jaspercurry/sand-cube/workbench/designs/deferred_integral_front_bottom_hatch/brief.md

# Deferred integral-front / bottom-hatch brief

That's awesome thank you. I think there's one more pair that I wanted. Maybe I already have it. You tell me.

I just want the latest version of the enclosure that has the baffle and the enclosure that fit together and that have the smooth seam on all four corners. I say this because I'm gonna use that one as the external package when I decide to put a hatch in the bottom of the face and try two different variants. This one is important because I wanna put it together and fuse those faces together and then get the seam gone but the overall package should remain the same, including the bottom corner part, because I think this is the right one too. If I'm going to have the baffle stay in place then I don't need the bottom flat face on the baffle or whatever. This is the one I'm going to use to power the hatch project. I need you to find that for me and write me one more little prompt with that as well.
