jaspercurry/sand-cube/workbench/designs/deferred_integral_front_bottom_hatch/feedback.md

# Feedback log

## 2026-07-22 — full-perimeter package inventory

- User identified a second enclosure direction: retain the original full
  exterior package and all four smooth/sculpted corners, make the front baffle
  permanent, remove the front seam, and later explore bottom-hatch variants.
- The latest surviving full-perimeter reference was identified as the
  `lightweight_coherent_closure` bucket, baffle, and installed assembly. The
  later flat-bottom/hybrid artifacts were explicitly excluded from this
  branch.
- Exact artifact paths, hashes, STEP checks, owning source, nested-seam
  ancestor, and build-freshness caveat were recorded in `source_manifest.md`.
- No existing source or CAD geometry was changed, rebuilt, fused, or rendered.
- The future prompt requires a source-level monolithic construction before the
  nested split, rather than a naïve union of separated STEP solids across the
  modeled gasket gap. It also defers tube/resonator repackaging until the
  integral enclosure and hatch architecture are accepted.
