jaspercurry/sand-cube/workbench/designs/deferred_port_tube_resonator/brief.md

# Deferred bass-reflex tube and resonator brief

The last thing is there are two other files that I think are really important to me:
- The tube iterations I've been doing for the base reflex port. That's really important and part of that but I think it's got a separate part of the file system. There's the resonator, right, and that's to help remove resonant frequencies. That is part of kind of the tube structure.
- Can you also find those and make a secondary prompt? Right now I don't want to mess with them. I just want to get all the code to help make them and get it set aside in a good spot. I'm going to come back to it once the fundamentals of the enclosure are nailed down and then we can manipulate the tubes and everything to fit the finalizing closure.
