jaspercurry/sand-cube/workbench/designs/deferred_port_tube_resonator/feedback.md

# Feedback log

## 2026-07-22 — deferred inventory

- User identified the bass-reflex tube iterations and the mode-suppressing
  resonator as important work to preserve but explicitly deferred all geometry
  changes until the enclosure and closure fundamentals are final.
- The tube lineage, resonator lineage, exact current working-tree source
  hashes, current integrated artifacts, latest Rev D artifacts, diagnostics,
  and the Rev C/Rev D integration boundary were recorded in
  `source_manifest.md`.
- Existing source was left in its cataloged experiment directories. No source
  was reset, moved, copied, or edited, and no CAD model, sidecar, viewer, or
  render was generated.
- A self-contained future-agent prompt was written to `resume_prompt.md` with
  a strict final-enclosure gate and measurable restart criteria.
