jaspercurry/sand-cube/workbench/designs/canonical_working_set/horn/links/horn_work_summary.md

../../../../../docs/horn-print-and-viewer-work-summary.md
