jaspercurry/sand-cube/workbench/designs/le_cleach_horn_190/variants/rollback_140/brief.md

# 140° variant — user brief

So you can see that we have a LeClesh horn or a bunch of LeClesh horn variants here in the repo. Could you look at them? I think there's one most recent one that we did actually use the proper LeClesh spreadsheet to inform and I'd love your help to make a new version of a LeClesh horn that matches the new external dimensions of the enclosure I'm working on.

That enclosure is still being revised but you'll see it in the folder and it's, I believe, 190 mm square so I need the diameter of our new LeClesh horn to also be 190 mm square. I'm using a base reflex tube now to hold up the compression drivers and mount and I think it means that the compression driver is going to potentially be a little bit farther back but maybe not actually. We're gonna keep the length of the horn as is for right now and then we'll revise the length and just update the calculation because I understand length is one of many inputs to the LeClesh function.

Let's just get started now. Maybe if you wanna engineer it in a way, you could solve for LeClesh horn with a given length and then that will make it easy to update in the future. Can you help me with this?
