jaspercurry/sand-cube/workbench/designs/le_cleach_horn_190/variants/rollback_140/feedback.md

# 140° variant feedback chronology

## 2026-07-23 — baseline identification

- The repository contains two different profile methods in
  `src/features/horn.py`: the older `legacy_recurrence` and the exact
  `le_cleach_2007` spreadsheet recurrence added in commit `d767489`.
- The stable `src/final_horn.py` still selects the older default method.
- The most recent matching horn is owned by the 190-by-190-by-210
  single-circular-port study. Its stored diagnostics report:
  - 190.0001119 mm physical rolled envelope;
  - 186.130 mm acoustic mouth;
  - 82.3821368 mm axial length;
  - 1002.0056 Hz solved profile cutoff;
  - wavefront factor T = 0.49437398987356584;
  - exact 2007 spreadsheet recurrence;
  - 0.0015091 mm maximum sampled spline deviation.
- Direction: preserve that geometry as the baseline, create a standalone
  candidate, and replace the hand-pinned T value with a deterministic solve
  from the named axial-length target.

## 2026-07-23 — standalone candidate checkpoint

- Production build job:
  `20260723T193247-build-f5f67ed6c8`.
  - Worker PID: 72479.
  - Elapsed: 23.225 seconds.
  - Peak RSS: 0.70 GiB.
  - Exit status: completed.
  - Published outputs: two.
  - Cleanup succeeded and no owned orphan processes remained.
- Exact artifact:
  `build/workbench/le_cleach_horn_190/le_cleach_horn_190.step`.
- STEP SHA-256:
  `56b793cb82df63e898ec8039e0353858817101880e84a87a588f9fb55f180df5`.
- The new inverse solve uses `target_axial_length` as the independent input and
  produced:
  - T = 0.49437398761510853;
  - profile cutoff = 1002.0055766296128 Hz;
  - axial length = 82.38213689951849 mm;
  - spreadsheet row step = 0.04623792275746711 mm;
  - 3020 exact recurrence samples.
- Geometry checks:
  - 190.0001119 mm maximum physical rolled envelope;
  - 186.130 mm acoustic mouth;
  - 8.000 degree CAD throat tangent;
  - 140.000 degree recurrence and CAD terminal tangent;
  - 0.0015091 mm maximum sampled recurrence-to-CAD spline deviation;
  - one valid solid before and after STEP round-trip;
  - exactly two 6.6 mm cylindrical bolt-hole faces, with the three-hole pattern
    disabled.
- STEP audit job `20260723T193323-audit-step-1bc2ce0d09` found one solid, one
  shell, 15 faces, zero boundary edges, zero non-manifold edges, no
  self-interference, and no offset surfaces.
- The hash-matched topology sidecar was regenerated by job
  `20260723T193340-text-to-cad-artifacts-a684077a1c`; it reports 15 mapped
  faces, 28 mapped edges, and zero unmapped surface edges.
- Agent visual review:
  - `snapshot-isometric_20260723T193351Z.png` shows a symmetric rolled-back
    flare, smooth throat-to-mouth shading, the intended two-hole flange, and
    no visible crack or surface collapse.
  - `snapshot-meridian-section_20260723T193404Z.png` shows the expected
    rolled-back meridian and constant wall, but the line renderer omits pieces
    of coincident/shared boundaries near the throat.
  - The final-STEP center-plane diagnostic
    `meridian_diagnostics.json` resolves that visual ambiguity: exactly two
    valid positive-area section faces and exactly two closed wires, one per
    side of the axis. The apparent section gaps are rendering omissions, not
    acoustic-path openings.
- Remaining design decision: driver and port-tower setback/placement remains
  intentionally unfrozen until the enclosure support revision is ready.

## 2026-07-23 — family promotion

- Reorganized entrypoint:
  `workbench/designs/le_cleach_horn_190/variants/rollback_140/build.py`.
- Reorganized artifact:
  `build/workbench/le_cleach_horn_190/variants/rollback_140/le_cleach_horn_190_rollback_140.step`.
- Build job `20260723T200810-build-13d1c87caa` completed successfully in
  22.172 seconds with 0.69 GiB peak RSS, published two outputs, cleaned its
  workspace, and left no owned orphan processes.
- Accepted dimensions, solver values, and topology were reproduced.
- Current STEP SHA-256:
  `3892b70ebf13550881996c886a40a01b1dc89d3132df7162dc935a15d1513fff`.
- Topology audit job `20260723T200914-audit-step-b3bda2ced0` passed.
- Sidecar job `20260723T200954-text-to-cad-artifacts-04704fc492` passed.
- Snapshot job `20260723T201018-text-to-cad-artifacts-957d407ae4`
  reproduced the accepted smooth, symmetric isometric appearance.
