jaspercurry/sand-cube/workbench/designs/le_cleach_horn_190/variants/rollback_160/brief.md

# 160° rollback variant — user brief

## User request

> How hard would it be to increase the rollback? I think right now it's got like a 140° angle for that rollback. What would a 160° look like? Would that be hard for you to do?

## Working interpretation

“Rollback” is the terminal wall angle measured from the horn axis, matching the
existing `exit_angle_deg` parameter. The current 140° horn remains the baseline;
this iteration creates a separate 160° comparison candidate.

## Frozen dimensions

- Physical X/Y envelope: 190.0 mm square
- Acoustic axial length: 82.38213681735276 mm
- Throat diameter: 25.4 mm
- Wall thickness: 3.2 mm
- Throat angle: 8°
- Existing DE250 two-hole mounting geometry
- Existing flange and throat-spigot geometry

Driver/enclosure placement is intentionally deferred. This comparison isolates
the rollback-angle change.
