jaspercurry/sand-cube/workbench/designs/canonical_working_set/acoustics/bass_reflex_tube/reference_evidence/manifest.md

# Bass-reflex tube reference evidence

These files are immutable, hash-bound review evidence copied from the
read-only intake checkout on 2026-07-22. They are not authoritative source.
The `Original SHA-256 = promoted SHA-256` column records both hashes; identity
was verified after the copy.

| File | Original repository path | Original SHA-256 = promoted SHA-256 | Bytes | Recorded producer | Approved semantic contribution | Caveat |
|---|---|---|---:|---|---|---|
| `sand_cube_190x210_single_oval_port_internal_tube.step` | `build/sand_cube_190x210_internal_squat_absorber_rear_corners_parabolic_side_g1_lightweight_coherent_closure/sand_cube_190x210_single_oval_port_internal_tube.step` | `5667fa455b81f8fc0f9a4645677a359f7b9072f0750eaff4f39a2099255fa19c` | 1,094,673 | Lightweight coherent-closure publication of the `sand_cube_190x210_single_oval_port` lineage | Selected internal oval tube geometry | Copied from a later enclosure build; use the recorded route-source chain to reproduce and compare |
| `diagnostics.json` | `build/sand_cube_190x210_internal_squat_absorber_rear_corners/diagnostics.json` | `dce0dcd3452ee8a98cea69073a52b3c3a299e42ec1a0e5bd716197cbf27af913` | 51,330 | `experiments/sand_cube_190x210_internal_squat_absorber_rear_corners/generate_sand_cube_190x210_internal_squat_absorber_rear_corners.py` | Route measurements for the selected rear-corner stage | Describes an earlier route stage, not the copied lightweight artifact; embedded absolute build paths are historical records, not portable links |
