jaspercurry/sand-cube/workbench/designs/canonical_working_set/enclosures/removable_front_baffle/reference_evidence/manifest.md

# Removable-front reference evidence

These files are immutable, hash-bound review evidence copied from the
read-only intake checkout on 2026-07-22. They are not authoritative source and
must not be treated as proof that the landed Python rebuilds identical
geometry. The `Original SHA-256 = promoted SHA-256` column records both hashes;
identity was verified after the copy.

| File | Original repository path | Original SHA-256 = promoted SHA-256 | Bytes | Recorded producer | Approved semantic contribution | Caveat |
|---|---|---|---:|---|---|---|
| `clean_corner_hunks_bucket.step` | `build/workbench/enclosure_baffle_recovery/clean_corner_hunks_candidate_viewer/clean_corner_hunks_bucket.step` | `eaeed68103e3110ca3e888ece90002a7f2f98a8b174fab5906e7fb0bd9350b97` | 4,310,535 | `workbench/designs/enclosure_baffle_recovery/build_step_derived_clean_hunks_candidate.py` | Curved seat with the four unwanted corner/fill-port hunks removed | STEP-derived disposable candidate; coordinated source build did not complete |
| `hybrid_seam_assembled.step` | `build/sand_cube_190x210_internal_squat_absorber_rear_corners_parabolic_side_g1_simple_tongue_groove_baffle/hybrid_seam_assembled.step` | `90558975e0e8fb735534b53a73eb7970d3bdddd6aeda34fb821380915877bab0` | 11,094,222 | Historical run of the simple tongue-and-groove lineage; exact producing source revision is not preserved | First/larger solid is the complementary flat-bottom bucket reference | Archived two-solid assembly; standalone extraction was invalid and was not published |
| `simple_tongue_groove_baffle.step` | `build/sand_cube_190x210_internal_squat_absorber_rear_corners_parabolic_side_g1_simple_tongue_groove_baffle/simple_tongue_groove_baffle.step` | `23c4d67927bbec6702c300c9912a7542383de093940378184b3d932fee3971c2` | 7,245,209 | `experiments/sand_cube_190x210_internal_squat_absorber_rear_corners_parabolic_side_g1_simple_tongue_groove_baffle/generate_sand_cube_190x210_internal_squat_absorber_rear_corners_parabolic_side_g1_simple_tongue_groove_baffle.py` | Genuinely planar full-width print edge and associated baffle material ownership | Approval does not extend to its tongue-and-groove or other seam details |
