jaspercurry/sand-cube/workbench/designs/canonical_working_set/brief.md

# Brief

> Yes that's exactly right. It's just a trustworthy design map, ideally with these fundamental atomic models and code or whatever moved to the directory that we can easily work on

The detailed design intent is already preserved verbatim in these existing
records and is incorporated here by reference:

- `workbench/designs/enclosure_baffle_recovery/brief.md`
- `workbench/designs/deferred_integral_front_bottom_hatch/brief.md`
- `workbench/designs/deferred_port_tube_resonator/brief.md`

This iteration organizes those accepted handoffs without changing geometry.
