jaspercurry/sand-cube/workbench/designs/canonical_working_set/acoustics/d_squat_resonator/reference_evidence/manifest.md

# D-squat resonator reference evidence

These files are immutable, hash-bound review evidence copied from the
read-only intake checkout on 2026-07-22. They are not authoritative source.
The `Original SHA-256 = promoted SHA-256` column records both hashes; identity
was verified after the copy.

| File | Original repository path | Original SHA-256 = promoted SHA-256 | Bytes | Recorded producer | Approved semantic contribution | Caveat |
|---|---|---|---:|---|---|---|
| `internal_d_squat_absorber_installed.step` | `build/sand_cube_190x210_internal_squat_absorber_rear_corners_parabolic_side_g1_lightweight_coherent_closure/internal_d_squat_absorber_installed.step` | `a16aeb1b440ef94a3cb208e4388eeac9c2acec238791fde4c33ebf0a3a4788ce` | 975,988 | Lightweight coherent-closure publication of the internal-absorber lineage | Rev C installed placement inside the enclosure | Placement evidence only; not a standalone manufacturing artifact |
| `port_absorber_d_squat_rev_d_assembly_finished_reference.step` | `build/sand_cube_190x210_port_absorber_slotted_d_squat_rev_d/port_absorber_d_squat_rev_d_assembly_finished_reference.step` | `3ed5020cf53511f676ec3ed9a709d44a81e112f5b91fb1757dfbf09f4fcb33da` | 953,398 | `experiments/sand_cube_190x210_port_absorber_slotted_d_squat_rev_d/generate_port_absorber_slotted_d_squat_rev_d.py` | Rev D assembled reference | Frozen comparison artifact; rebuild identity not checked during intake |
| `port_absorber_d_squat_rev_d_print_layout.step` | `build/sand_cube_190x210_port_absorber_slotted_d_squat_rev_d/port_absorber_d_squat_rev_d_print_layout.step` | `5936001348ce7d146519a8836507d6800b703cce71f0a3d808f2df20f818d76e` | 811,849 | Same Rev D generator | Rev D print-layout reference | Layout reference only; no slicer settings are implied |
| `diagnostics.json` | `build/sand_cube_190x210_port_absorber_slotted_d_squat_rev_d/diagnostics.json` | `b2486dd92bda832be28b2d1e0b54666c06e0641924a2231283b8c37717a28c01` | 18,725 | Same Rev D generator | Exact recorded Rev D branch inputs and measurements | Describes the copied output, not a fresh landing build |
