jaspercurry/sand-cube/workbench/designs/canonical_working_set/enclosures/integral_front_bottom_hatch/reference_evidence/manifest.md

# Integral-front / bottom-hatch reference evidence

These files are immutable, hash-bound review evidence copied from the
read-only intake checkout on 2026-07-22. They are not authoritative source and
the landed generator is newer than these artifacts. The
`Original SHA-256 = promoted SHA-256` column records both hashes; identity was
verified after the copy.

| File | Original repository path | Original SHA-256 = promoted SHA-256 | Bytes | Recorded producer | Approved semantic contribution | Caveat |
|---|---|---|---:|---|---|---|
| `centered_captive_nut_bucket.step` | `build/sand_cube_190x210_internal_squat_absorber_rear_corners_parabolic_side_g1_lightweight_coherent_closure/centered_captive_nut_bucket.step` | `39e6b2d95317d2348afd992ceda2e98d16a383820a3846737e21228ef1c41486` | 4,583,193 | `experiments/sand_cube_190x210_internal_squat_absorber_rear_corners_parabolic_side_g1_lightweight_coherent_closure/generate_sand_cube_190x210_internal_squat_absorber_rear_corners_parabolic_side_g1_lightweight_coherent_closure.py` | Full-perimeter bucket reference | Hash-bound review output from a coordinated job whose later preview-only cutaway failed |
| `centered_captive_nut_baffle.step` | `build/sand_cube_190x210_internal_squat_absorber_rear_corners_parabolic_side_g1_lightweight_coherent_closure/centered_captive_nut_baffle.step` | `1dd518458c8fed6792c4acd91f0717b353288c18e49c5b1c6ba31f2c9cc6af03` | 8,687,475 | Same lightweight coherent-closure generator | Full-perimeter baffle reference | One valid solid, but source/artifact identity has not been re-established |
| `centered_captive_nut_assembled.step` | `build/sand_cube_190x210_internal_squat_absorber_rear_corners_parabolic_side_g1_lightweight_coherent_closure/centered_captive_nut_assembled.step` | `4595684887c4fb239dd8fefaeb7307a797c3673281df19f3d709b659b3440bf2` | 13,810,764 | Same lightweight coherent-closure generator | Installed-fit reference | Nine valid solids include gasket and hardware references; not a print part |
| `diagnostics.json` | `build/sand_cube_190x210_internal_squat_absorber_rear_corners_parabolic_side_g1_lightweight_coherent_closure/diagnostics.json` | `7194ac15b3c78e272ae60d9b1115be6129f0fdfbfd7cbfdcef32593cddbff04d` | 70,504 | Same lightweight coherent-closure generator | Recorded geometry, installed-volume, and tuning measurements for this evidence set | Describes the copied output, not a fresh landing build; embedded absolute build paths are historical records, not portable links |
