jaspercurry/sand-cube/objects/GX16.stp

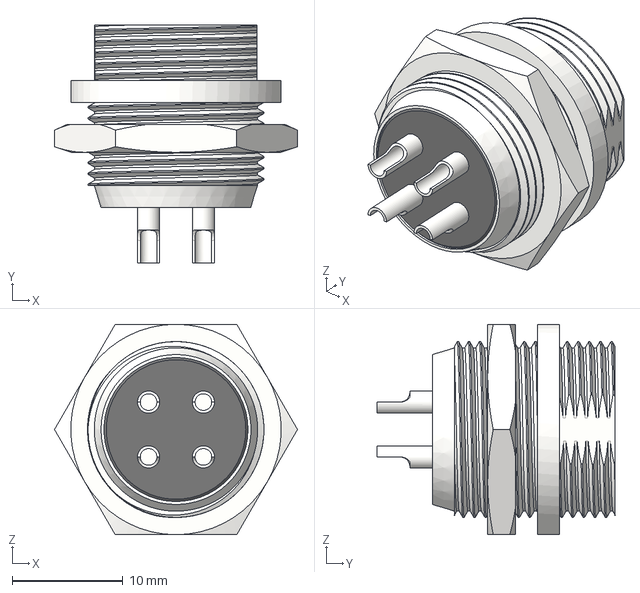
[picture p8: CAD file, 2026-05-16]
objects/GX16.stp
21.9 x 21.5 x 19.0 mm
