jaspercurry/sand-cube/objects/E180HE-PR.step

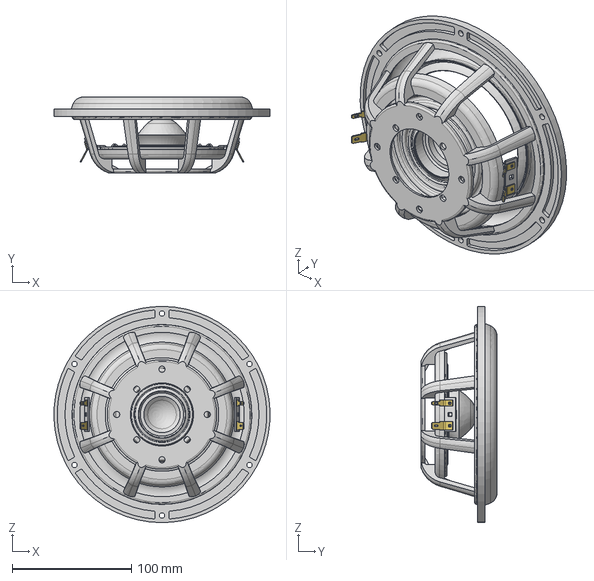
[picture p9: CAD file, 2026-05-16]
objects/E180HE-PR.step
181.4 x 64.0 x 181.5 mm
