jaspercurry/sand-cube/objects/E150HE-44.step

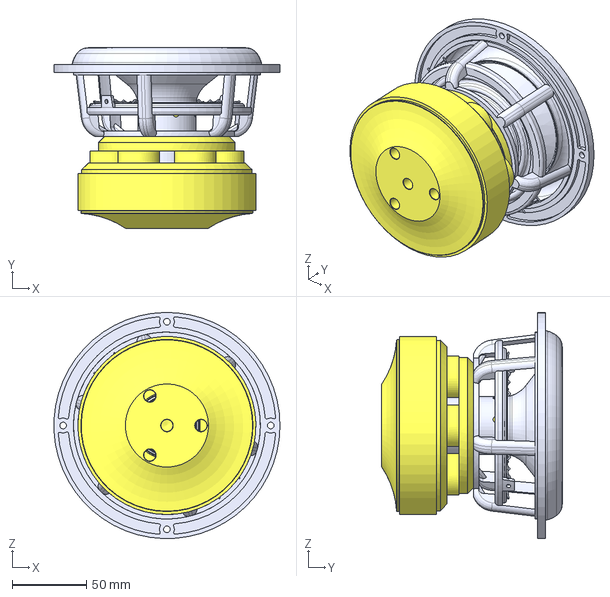
[picture p10: CAD file, 2026-05-16]
objects/E150HE-44.step
152.4 x 121.7 x 152.4 mm
6_0_____CAST_BFGT__0502A__REV_
38MM_VCDDGATE_REV-A1_A_
