jaspercurry/sand-cube/workbench/designs/cad_feedback_loop_rollout/baseline-step-sha256.txt

# cad_runner job 20260723T211801-generate-sand-cube-190x210-single-oval-port-43ef802b42
# elapsed_seconds=105.594 peak_rss_bytes=885719040 cleanup_reaped=true orphans=0
24aaafefc60ea8238387eda621a12f7032a976b9188f46074b07b13557281170  sand_cube_190x210_single_oval_port_airway.step
d2c9fd17aabc00872acaa5be44ef441448414dafe2ca892b0e238d612991c1ab  sand_cube_190x210_single_oval_port_assembly.step
c17d0cca77e7d6511208e47e2d88b29f5db16450701179dea7fc73e638ddfbcf  sand_cube_190x210_single_oval_port_base.step
9fbc8a8fa89885bc039d770e2adb8f656937f64abc07ef26626db2d13dcee0e6  sand_cube_190x210_single_oval_port_cutaway.step
1eded4b9dbb2024c458eacac672d0171ea5e3b9c020a4288703b839c4cc6b5ee  sand_cube_190x210_single_oval_port_gx16.step
7ab03b2d47b9a56e9d0683fd22d489a1926dfea0171c865913ad98613fba6d2a  sand_cube_190x210_single_oval_port_hardware_check.step
d57ad948c78ecf9863ef34f7386df557dd5d2980e16d1ca6ab15d5596d3bbd18  sand_cube_190x210_single_oval_port_horn.step
aa3d88f1fabd3380dd585740d99e04c962fddda5c6d0883d536e1b3d038fcfb8  sand_cube_190x210_single_oval_port_internal_tube.step
80dc810c5478aa5d6305cd482ae8f11e18c1cc125b376f5274c5cfab621c1662  sand_cube_190x210_single_oval_port_tower.step
