jaspercurry/sand-cube/experiments/sand_cube_190x210_internal_squat_absorber_rear_corners/README.md

# Rear-corner sweep / exact rear-flush absorber variant

This isolated variant preserves all preceding studies. It routes the 40 mm
circular port through a broad R75 lower-left rear sweep and an R50 lower-right
rear rise, then uses four rotated R35.7 elbows around the unmodified 56 mm squat
absorber cartridge.

The absorber D-flat has exact nominal contact with the rear acoustic face. No
printing relief, absorber mounting tab, or enclosure mounting node is modeled.
