jaspercurry/sand-cube/workbench/designs/atomic_characterization_refactor/README.md

# Atomic characterization/refactor

Status: **Phase B implementation, strict final acceptance, exact visual review,
and independent adversarial re-review are complete with no unresolved
actionable findings in the agreed landing scope.**

The user accepted the Phase A visual evidence and authorized Phase B. The
metadata-only `family.coordinate_contract` pilot is complete. The user then
explicitly instructed the agent to record but not pause at later checkpoints.
No removable-front references have been reconciled, no Variant I geometry has
been created, and no deferred component has been integrated.

## Governing records

- `brief.md` — verbatim user request; do not edit
- `contract.md` — interpreted operational boundary
- `feedback.md` — chronological work log
- `atomic_manifest.json` — authoritative input, atom, evidence and checkpoint
  description
- `workflow-card.md` — concise resume state for the current implementation
- `current-baseline-evidence.json` — durable current-base fit/equivalence facts
- `variant-r-producer-source-closure.json` — committed projection of the exact
  authoritative-input producer, toolchain and complete live source closure
- `variant-r-release-source-closure.json` — committed projection of the exact
  release commit, release-job JSON, nine bound model artifacts and all loaded
  release dependencies
- `final-acceptance-evidence.json` — compact final jobs, measurements, hashes,
  visual provenance and review disposition
- `independent-review.md` — initial findings, amendments, and final
  no-unresolved-findings disposition
- `render_phase_a_reports.py` — deterministic Markdown projection
- `coordinate_contract.json` — staged verification contract for the first atom

## Generated checkpoint views

- `inventory.md`
- `atomic_map.md`
- `compatibility_matrix.md`
- `dependency_graph.md`
- `baseline_report.md`
- `printability_report.md`
- `pilot_report.md`

## Architecture proposal

- `proposed_architecture.md`

## Current geometry boundary

The failed rail reproduction recorded during the earlier Phase B pilot is
historical. Commits through `789cf7f` repaired that deterministic failure and
established the current flat-bottom Variant R closure. On exact combined base
`c25cddb`, the active Python source and validator reproduce the accepted bucket,
baffle, and six protected sections with zero bidirectional material difference
at `1e-5 mm³`, matching topology and mass properties, zero overlap, and passing
STEP round-trips.

The cataloged `scripts/generate_variant_r.py` entrypoint makes the formerly
ignored base input portable. It extracts exact geometry commit `789cf7f`,
applies one hash-bound capture-only overlay at the accepted construction
boundary, verifies the complete STEP DATA section, reproduces the accepted
file serialization, and publishes both the base and a current attestation
through `cad_runner`. The latest producer binds 57 loaded repository sources,
including all 33 loaded generator stages. Release evidence is collected only
after geometry in a separate observational job, preserving the exact accepted
validator execution path. It binds release commit `d114d79`, the exact release
job record, nine model artifacts, 62 loaded repository sources, 58
geometry/parameter sources and all 33 loaded generator stages. Every dependency
byte is verified at that commit. The historical release job did not itself
record whole-tree cleanliness, and the committed record says so instead of
inventing that claim. The final strict job passes both complete parts and six
protected sections with zero bidirectional material delta and unchanged
diagnostics. Committed closure projections preserve those exact facts without
treating ignored `build/` files as current.

The active architecture has explicit owners for datums, pure parameters,
print contracts, Variant R seam/bottom composition, the independent future
Variant I interface, generated input/provenance, deterministic measurements,
native-free equivalence policy, STEP export/round-trip, artifacts, verification
and thin entrypoints. Variant I has no geometry and imports no Variant R owner.

The refactor's accepted geometry intentionally preserved its historical flat-
bottom relationship. A separate, explicitly authorized production iteration
has since replaced the whole-part splice with the continuous exact-edge donor
and a baffle-only sole trim. Its exact twelve internal bucket-only
micro-omissions are recorded fail-closed in
`workbench/designs/variant_r_no_splice_production/`; the refactor evidence here
remains the immutable pre-correction baseline.
