jaspercurry/sand-cube/workbench/designs/atomic_characterization_refactor/atomic_map.md

<!-- Generated by render_phase_a_reports.py from atomic_manifest.json. Do not edit by hand. -->

# Atomic ownership map

Authority: `atomic_manifest.json`.

Current execution overlay: **FINAL FORCED RELEASE EQUIVALENT; VISUAL EVIDENCE INSPECTED; INDEPENDENT REVIEW PENDING**. Rows retain historical characterization; the overlay supersedes old operational blocker wording.

| Semantic ID | Owner | Current owner/source | Dependencies | Mates | Baseline | Shareability | Readiness | Conflicts |
|---|---|---|---|---|---|---|---|---|
| family.coordinate_contract | shared enclosure-family layer | src/enclosure_family/datums.py | — | — | native-free coordinate contract and full current Variant R strict release pass | yes; one explicit 190x210 family datum owner now exists | implemented and verified | legacy 203 mm project parameters are a different family contract |
| family.exterior_envelope | Variant R foundation; possible family sharing remains unproved | immutable accepted foundation producer plus explicit Variant R composition | family.coordinate_contract | — | current Variant R full-part bounds/topology/mass and zero-material-delta proof pass | intended, not yet proven semantically identical | verified for Variant R; do not promote to shared geometry until an independent Variant I proves identical semantics | legacy 203 mm production enclosure and 222.463 mm horn mouth belong to different packages |
| family.exterior_shell | Variant R foundation; possible family sharing remains unproved | immutable accepted foundation producer behind VariantRFoundation | family.coordinate_contract<br>family.exterior_envelope | — | current Variant R complete bucket and protected sections pass strict equivalence | possible only if Variant I exterior is proven identical | verified for Variant R; family extraction is deferred until cross-variant semantic identity can be proved | root project 3/12/3 contract is not this 2/3/2 study stack |
| family.inner_wall_sand_void | Variant R foundation; future sharing unproved | single-oval-port base and conformal-inner-wall stage | family.exterior_shell | family.fill_blisters_passages | current Variant R validator proves zero fill blockage, closed non-fill sand cap and exact protected geometry | intended but unproved | verified as current Variant R foundation behavior; not promoted as shared Variant I geometry | 3 mm void differs from repository legacy 12 mm void |
| family.rear_face | Variant R foundation with Variant R print-contract consumer | single-oval-port base plus rear-corner/conformal detail | family.exterior_shell<br>family.inner_wall_sand_void | — | current Variant R bounds and rear-body retention diagnostics pass | geometry may be shared; print semantics are variant-specific | verified for Variant R; print semantics remain variant-specific | future I does not use rear face as bed datum |
| R.front_service_opening | Variant R | VariantRFoundation implemented by the active compatibility adapter and consumed by src/enclosure_family/variant_r/assembly.py | family.exterior_shell<br>family.inner_wall_sand_void | R.baffle_body<br>R.front_bulkhead_gasket_support | current bucket/baffle parts, service opening retention diagnostics and protected sections pass | no | verified Variant R foundation boundary | accepted lower boundary is preserved exactly; correction is a later geometry task |
| R.front_bulkhead_gasket_support | Variant R | VariantRFoundation implemented by the active compatibility adapter; verification policy in src/enclosure_family/variant_r/verification.py | R.front_service_opening<br>family.inner_wall_sand_void | R.baffle_body<br>R.gasket_land_compression | current gasket support ratios are 1.0 against a 0.985 minimum; corner and fill checks pass | no; removable-joint support | verified Variant R foundation boundary | physical gasket compression and printed support behavior remain untested |
| R.sculpted_lrt_seam | Variant R | src/enclosure_family/variant_r/seam.py composed by src/enclosure_family/variant_r/assembly.py | R.front_service_opening<br>R.front_bulkhead_gasket_support | R.baffle_body<br>R.gasket_land_compression | current source generation plus strict zero-material-delta proof for full parts and protected seam sections | no | extracted and strict-equivalence verified | the accepted current flat-bottom imperfection is protected baseline behavior |
| R.bottom_material_ownership | Variant R | src/enclosure_family/variant_r/bottom_ownership.py composed by src/enclosure_family/variant_r/assembly.py | R.front_service_opening<br>family.exterior_shell | R.baffle_body | current source generation plus strict zero-material-delta proof for full parts and flat-bottom/corner protected sections | no | extracted and strict-equivalence verified | accepted current missing-material relationship remains intentionally unfixed |
| R.baffle_body | Variant R | src/enclosure_family/variant_r/assembly.py over VariantRFoundation, seam.py and bottom_ownership.py | R.sculpted_lrt_seam<br>R.bottom_material_ownership<br>family.driver_interface | R.front_service_opening<br>R.front_bulkhead_gasket_support | one valid solid; strict topology/bounds/volume/area/center-of-mass and zero-material-delta proof pass | no | current Variant R geometry verified | accepted flat-bottom/missing-material relationship remains intentionally unfixed |
| R.flat_baffle_print_edge | Variant R | src/enclosure_family/variant_r/bottom_ownership.py with print contract in variant_r/print_contracts.py | R.baffle_body<br>R.bottom_material_ownership | — | current bottom section is strict-equivalent; planar contact area is 2277.9500229303967 mm2 with brim assumed | no | geometry and analytic contact verified; physical adhesion unverified | known missing-material relationship is preserved |
| family.driver_interface | current Variant R foundation; future family sharing unproved | hooked/lightweight baffle and fairing ancestors | family.coordinate_contract | deferred.horn_interface<br>deferred.bracket_interface | current baffle bore/fairing geometry is included in the strict full-part equivalence proof | intended if both variants use the same driver and front profile | verified for current Variant R only | future horn package not accepted |
| R.gasket_land_compression | Variant R | VariantRFoundation plus src/enclosure_family/variant_r/parameters.py and verification.py | R.sculpted_lrt_seam<br>R.front_bulkhead_gasket_support<br>R.baffle_body | R.sculpted_lrt_seam<br>R.baffle_body | 1.0 mm compression knob and 1.0/1.0 bucket/baffle support ratios reproduce current diagnostics exactly | no | geometry verified; physical gasket behavior unverified | material compression specification and leak test remain absent |
| R.corner_sealing | Variant R | VariantRFoundation with deterministic checks in the current validator | R.front_bulkhead_gasket_support<br>R.gasket_land_compression | family.fill_blisters_passages | zero unclosed outside-gasket and baffle-corner volumes; four baffle corner closures | no | current Variant R geometry verified | physical sealing remains untested |
| family.fill_blisters_passages | current Variant R foundation; future variant-specific termination remains separate | front-fill perimeter-seal and lightweight closure | family.inner_wall_sand_void<br>R.front_bulkhead_gasket_support | family.inner_wall_sand_void<br>R.corner_sealing | current fill passage blockage is 0.0 mm3 and both passages reach the live sand void | shared upstream routing only if termination semantics are separated | verified for current Variant R; not promoted as shared Variant I geometry | front termination differs fundamentally between removable and integral fronts |
| family.braces_supports | current Variant R immutable foundation; future shared ownership unproved | conformal_full_system and lightweight _coherent_internal_braces | family.inner_wall_sand_void<br>deferred.tube_interface | family.inner_wall_sand_void | the accepted coherent-brace foundation is reproduced exactly by the portable producer and retained by the current bucket | not proven; front supports differ by variant | verified for current Variant R foundation; no shared Variant I brace owner is asserted | physical support/print behavior remains unverified |
| family.support_sensitive_transitions | family metadata candidate | not explicit; distributed across bulkhead, fairing, rails and fill passages | family.braces_supports<br>family.fill_blisters_passages | — | visual/section characterization only | neutral predicates can be shared; geometry is variant-specific | metadata-only candidate | current sources do not encode a common printable-overhang policy |
| R.bucket_print_contract | Variant R | src/enclosure_family/variant_r/print_contracts.py | family.rear_face<br>family.support_sensitive_transitions<br>R.front_service_opening | — | explicit rear-face-down metadata matches the accepted current artifact; physical seating footprint/flatness remains unverified | no | implemented metadata; physical print unverified | physical print and slicer behavior remain unverified |
| R.baffle_print_contract | Variant R | src/enclosure_family/variant_r/print_contracts.py | R.flat_baffle_print_edge<br>family.support_sensitive_transitions | — | explicit +Z/brim metadata plus measured Z=-91.5 mm contact plane, 2277.9500229303967 mm2 planar area and 187.02097935912883 mm X span | no | implemented and analytically verified; physical print unverified | physical adhesion and slicer behavior remain unverified |
| I.integral_front | Variant I | src/enclosure_family/variant_i/interface.py declares the future independent boundary; geometry intentionally absent | family.exterior_shell<br>family.driver_interface<br>family.fill_blisters_passages | — | does not exist; references are removable-front evidence only | variant-specific composition | future geometry | historic full-perimeter assembly still has separate bucket/baffle and joint hardware |
| I.open_bottom | Variant I | src/enclosure_family/variant_i/interface.py declares future ownership only | I.integral_front<br>family.inner_wall_sand_void | I.hatch_interface | none | no | future geometry | no selected artifact contains this opening |
| I.hatch_interface | Variant I | src/enclosure_family/variant_i/interface.py declares future ownership only | I.open_bottom | I.open_bottom | none | no | future interface only | hatch design expressly outside Phase A/B |
| I.print_contract | Variant I | src/enclosure_family/variant_i/interface.py | I.open_bottom<br>family.support_sensitive_transitions | — | future metadata only; no geometry baseline claimed | no | implemented future metadata; geometry absent | historic references are closed-bottom removable assemblies |
| R.hinge_interface | Variant R | future Variant R owner | R.sculpted_lrt_seam<br>R.baffle_body | R.baffle_body | none; current leaf flags hinge false | no | future interface only | no hinge geometry approved |
| R.fastener_interface | Variant R | future Variant R owner; historical fastener stages are supporting only | R.bottom_material_ownership<br>R.gasket_land_compression | R.baffle_body | historic hardware reference only; current leaf flags screws false | no | future interface only | historical captive-nut geometry is not accepted final behavior |
| deferred.horn_interface | deferred horn owner | src/final_horn.py and src/features/horn.py | family.exterior_envelope<br>family.driver_interface | family.driver_interface<br>deferred.bracket_interface | formula/source reference only; no selected STEP | external interface only | deferred | current mouth exceeds selected 190 mm width |
| deferred.tube_interface | deferred tube owner | rear-corner route source and tube ancestor chain | family.inner_wall_sand_void<br>family.rear_face | deferred.resonator_interface | historic artifact measured; current source/artifact parameter freshness unresolved | external interface only | deferred | historic 40 mm diagnostics versus current approximately 39.24 mm equivalent source parameter |
| deferred.resonator_interface | deferred resonator owner | Rev C modules and Rev D study generator | deferred.tube_interface | deferred.tube_interface | historic STEP/diagnostics measured; sources not run because component is deferred | external interface only | deferred | Rev D is not automatic mechanical replacement for Rev C |
| deferred.bracket_interface | deferred bracket owner | src/features/bracket.py | family.driver_interface<br>deferred.horn_interface | family.driver_interface<br>deferred.horn_interface | not selected for Phase A artifact inventory | external interface only | deferred | future horn/enclosure package unknown |
| deferred.electronics_interface | deferred electronics owner | not selected in canonical enclosure inputs | family.exterior_shell<br>family.inner_wall_sand_void | — | none in Phase A scope | external interface only | deferred | no accepted enclosure package |

Protected invariants, tolerances, print implications, consumers, and candidate references remain in the manifest to keep this view compact.
