jaspercurry/sand-cube/workbench/designs/atomic_characterization_refactor/feedback.md

# Atomic characterization/refactor feedback

This is the chronological Phase A record. Findings below are descriptive; the
authoritative structured facts are in `atomic_manifest.json`.

## 2026-07-23 — task and prompt integrity

- Work began only in the dedicated Codex worktree at
  `/Users/jaspercurry/.codex/worktrees/8b9b/CAD - Enclosure`.
- `HEAD` was
  `905ef31a0bea348b6805a2ef215c75b5a9592168`, the tip used for
  `codex/atomic-characterization-base`; the worktree itself is detached and
  the branch remains checked out in its separate base worktree.
- Local `main` is
  `ea5539f3372e1bad5ad05eba85f4bd9a53e8c868`, and that required commit is an
  ancestor of the task commit.
- The input-landing commit
  `2c94314b8cee90c3733991d48143375227a7d6b8` and its selected files were
  present.
- The complete `brief.md` was read. Its SHA-256 matched
  `7cb5fad7514df1670ba9fd017cce0d44369564018515e3b4ec5be2c55d4bb96e`.
  It was not modified.

## 2026-07-23 — skill, rules and canonical inputs

- The repository-local `speaker-enclosure-cad` skill and its iteration,
  visual-review, toolchain-safety, model-catalog and geometry-gotcha
  references were read and applied.
- Root/scoped `AGENTS.md`, project/catalog/contract files, development and
  verification documentation, every canonical working-set root/component
  document, the complete enclosure recovery record, all selected manifests,
  the active owner/validator/handoff and relevant generator ancestry were read.
- The canonical README/manifests now describe the landed inputs as committed
  and self-contained. Historic feedback retains historic dirty-checkout
  wording for provenance; it is not a current source statement and was not
  rewritten.
- Verification of `reference_checksums.sha256` passed all 30 selected paths.

## 2026-07-23 — pinned tool preflight

- The task reused Python 3.12.13, build123d 0.11.1 and OCP 7.9.3.1 from the
  existing repository virtual environment. No package was upgraded.
- This clean worktree initially lacked ignored local tool state. The exact
  pinned Text-to-CAD 0.3.9 checkout at commit
  `fdbb4b4fb62d95ae298cfe9a46fdc7092bdaf423` was cloned locally into ignored
  `build/` state; its already-installed Viewer and Snapshot runtimes were
  linked from the exact existing checkout. No network download or source-tree
  dependency change occurred.
- `scripts/cad_review.py doctor` passed all pins, catalog, read-only Viewer
  overlay and preferred-port checks.
- Catalog validation passed: 10 primary models and 38 experiment families.
- The native-free lightweight suite passed 82 tests and 19 subtests, including
  76 entrypoint-safety checks.

## 2026-07-23 — ownership and mutation characterization

- The apparent leaf owner is not self-contained. It aliases deep experiment
  modules, temporarily replaces perimeter/joint constants and functions, calls
  the complete ancestor `generate()` chain, and restores globals afterward.
- The semantic pre-split branch is the `full_base` argument entering
  lightweight `_lightweight_common_joint`. That function creates nominal and
  clearance envelopes, partitions bucket and baffle, and then adds gasket
  support, bulkhead, fill paths, bridges and braces.
- Current removable-joint dimensions are distributed: simplified closure owns
  sculpted path values and the corrected 184.3 mm/r7 broad reset; hooked owns
  bed/gasket/shoulder helpers; nested owns the 0.28 mm split envelope;
  lightweight patches the leaf gap to 1.0 mm and owns the bulkhead/support
  composition.
- This confirms that a future Variant I owner must branch semantically before
  the removable partition. The selected “integral” STEP set is still a
  removable bucket, baffle, gasket/hardware assembly and cannot be treated as
  Variant I geometry.

## 2026-07-23 — immutable reference measurements

- Ten selected STEP artifacts were imported and measured read-only with
  Build123d Workbench. Exact volume, surface area, bounds, center of mass and
  topology are recorded in `atomic_manifest.json` and projected into
  `baseline_report.md`.
- The clean bucket is one valid solid at `1,091,181.8588 mm³`; the hybrid
  bottom-ownership assembly is two valid solids, with a
  `1,111,212.8535 mm³` larger bucket and `233,360.5156 mm³` baffle.
- The selected flat baffle is one valid `231,910.4722 mm³` solid spanning
  approximately 190.0021 mm in X. Its accepted contribution remains the
  documented flat full-width edge; the measurement did not independently
  establish a continuous stable bed-contact face and minimum seating area.
- Tube and Rev C/Rev D references measured as valid multi-solid evidence.
  Their geometry was not integrated or refactored.

## 2026-07-23 — source reproduction gate

- A first runner invocation contained an incorrect shortened experiment path
  and stopped before loading source. It is not a CAD result.
- The corrected, catalog-resolved lightweight source was run once through
  `cad_runner` as job
  `20260723T040911-generate-sand-cube-190x210-internal-squat-absorb-603368ef69`.
- After 83.797 seconds and peak RSS 1,290,780,672 bytes, the current source
  failed with:
  `ValueError: rear-ramped longitudinal top rail did not produce one valid solid: 2`.
- The runner published no outputs and reaped its process group. There was no
  blind geometry retry.
- Because the authoritative lightweight base STEP was not produced, the leaf
  validator was not run. The accepted source baseline is therefore
  unreproducible at this commit. Immutable STEP references remain evidence and
  were not promoted as source.

## 2026-07-23 — exact visual evidence

- A byte-identical copy of the clean-bucket STEP was placed under ignored
  `build/workbench/atomic_characterization_refactor/near_perfect_bucket/`.
  It retains SHA-256
  `eaeed68103e3110ca3e888ece90002a7f2f98a8b174fab5906e7fb0bd9350b97`.
- Its Text-to-CAD sidecar has SHA-256
  `609bb53774ab6301a4ad724aeb62d0a0ed7b3600c93528d9502d73d8e5dc5d4b`.
- Initial Snapshot job
  `20260723T042549-text-to-cad-artifacts-55fbbd24c2` stopped before rendering
  because the ignored clean-worktree checkout lacked the already-installed
  pinned Snapshot runtime. After linking that exact runtime, sandboxed job
  `20260723T042612-text-to-cad-artifacts-88542cfab5` was cleanly reaped when
  macOS denied Chromium's MachPort rendezvous. Neither attempt produced an
  image or changed geometry.
- Snapshot job
  `20260723T042632-text-to-cad-artifacts-fe2639776f` completed in 3.095 seconds
  at peak RSS 856,621,056 bytes and produced an isometric plus one YZ center
  section from the same STEP/sidecar.
- The agent inspected both images. The isometric shows one coherent open-front
  bucket, the sculpted perimeter seat, top opening, internal rails/posts and no
  four repeated front corner hunks. The center section shows nested wall/shell
  outlines and isolated ledges, but does not prove gasket compression, lower
  ownership or printable overhang angles.
- A hash-bound read-only Viewer record was written under ignored build
  evidence. No transient Viewer selection token was used as source logic.

## 2026-07-23 — checkpoint decision

- `atomic_manifest.json` records 30 selected inputs and 30 semantic atoms.
- The generated inventory, atom map, compatibility matrix, dependency graph,
  baseline report and printability report all derive from that manifest.
- Phase B is blocked by both the required user gate and the failed source
  baseline. Variant R candidate reconciliation, Variant I geometry, acoustic
  integration and printability redesign remain later work.
- The proposed first pilot after explicit approval is the metadata-only
  `family.coordinate_contract`; no geometry atom should be extracted until the
  source baseline is repaired or an accepted reproducible source boundary is
  deliberately selected.

## 2026-07-23 — Viewer frontend repair

- The user reported that the hash-bound Viewer URL displayed `Not found`.
- The read-only 0.3.9 backend, exact STEP, and exact sidecar were all present.
  Browser inspection was used only because the failure was visible UI routing
  behavior that the server metadata endpoint could not diagnose.
- The clean worktree's ignored pinned Viewer checkout lacked its prebuilt
  `viewer/dist` frontend. The exact existing 0.3.9 frontend from the repository
  tool checkout was linked into that ignored checkout; no package, source,
  geometry, STEP, or sidecar changed.
- After reloading the same tab, the Viewer displayed
  `near_perfect_bucket.step`, its STEP tree, view controls, and release 0.3.9.

## 2026-07-23 — Characterization Checkpoint approved

- The user inspected the hash-bound `near_perfect_bucket.step` in the repaired
  read-only Viewer, said it looked good, and authorized the work to proceed.
- This approval opened Phase B. It did not make the failed source baseline
  reproducible and did not authorize geometry synthesis from STEP evidence.
- The first atom remained the proposed metadata-only
  `family.coordinate_contract`.

## 2026-07-23 — coordinate-contract pilot

- Added the native-CAD-free owner `src/enclosure_family/datums.py` for units,
  the 190x210x190 envelope, the +10 mm Y center, named planes, and axis
  polarity.
- The base `Design` now consumes that owner. Existing 190x210 source consumers
  use `Design.center_y` instead of duplicating the +10 mm datum.
- The fast contract validated eight selected requirements in 0.079 seconds at
  30,720,000 bytes peak RSS.
- The complete lightweight suite passed 86 tests and 19 subtests, catalog
  consistency, 76 entrypoint checks, and lint in 5.086 seconds at 59,359,232
  bytes peak RSS.
- Controlled native comparison job
  `20260723T100534-generate-sand-cube-190x210-internal-squat-absorb-c4d37f5ec2`
  failed after 95.849 seconds at 1,288,798,208 bytes peak RSS with the exact
  pre-existing invariant:
  `ValueError: rear-ramped longitudinal top rail did not produce one valid solid: 2`.
- The run published no outputs. It provides same-boundary evidence for the
  metadata refactor, not geometry equivalence.
- The user-accepted frozen STEP and Snapshot remain unchanged continuity
  evidence. No after-STEP or visual delta exists while the source baseline
  fails.

## 2026-07-23 — checkpoint-pause override

- The user explicitly instructed the agent not to keep stopping at checkpoints,
  to attempt the full saved brief, and to re-read the original prompt after
  context compression.
- Subsequent checkpoints will be recorded without pausing. Genuine
  safety/equivalence blockers still remain stop conditions.

## 2026-07-23 — exploratory baseline repair and equivalence stop

- After a context compression, the complete `brief.md` was read again and its
  SHA-256 again matched
  `7cb5fad7514df1670ba9fd017cce0d44369564018515e3b4ec5be2c55d4bb96e`.
- Scratch Workbench measurement showed that the rear ramp was already located
  at its intended design-coordinate Y/Z envelope before a second placement was
  applied. An uncommitted correction cleared the original two-solid rail
  failure and allowed the leaf base STEP to be exported for diagnosis.
- The experiments remained outside the accepted source boundary. The resulting
  leaf base STEP has SHA-256
  `2b00cc4f7c0d9203758893ffcab2039325d072070fb33c94f001b47ef9b09203`
  and is explicitly diagnostic evidence, not an accepted baseline.
- Fit job
  `20260723T111344-validate-simple-tongue-groove-baffle-51e3ab94c6`
  then failed the protected top-seam occupancy gate at two of 1,248 samples;
  the first point was `[-45.0, -71.75, 86.25]` mm.
- Focused diagnostic job
  `20260723T113000-diagnose-seam-identity-34754b3ab1` completed in
  384.514 seconds at 1,402,896,384 bytes peak RSS. Nine of 75 nearby samples
  confirmed the same direction: the authoritative bucket contains material
  where the flat-bottom hybrid bucket does not.
- In a 4 mm cube around the first mismatch, the authoritative bucket occupied
  `35.80665201146918 mm³`, the hybrid occupied `35.40168722922 mm³`, and their
  overlap equaled the hybrid volume. The reference-only difference was
  `0.40496478224918064 mm³`; the hybrid-only difference was zero.
- Both local diagnostic sections were one valid solid after STEP round-trip.
  Their exact paths and hashes are recorded in `atomic_manifest.json`.
- This is material geometry drift, not a matching-boundary or serialization
  artifact. Correcting it would reconcile the authoritative sculpted seam with
  the flat-bottom reference, which the brief reserves for later synthesis.
- Every exploratory source, viewer-adapter, alias, and validator edit was
  reverted. The committed coordinate-contract pilot remains the only Phase B
  source change.

## 2026-07-23 — current combined-base baseline reproduced

- Started from exact combined base
  `c25cddb3eeafe6f6dff3b551be4ceb53d5aee9ce`; current geometry lineage
  `789cf7fb4f63d9567585198c47bc3b5b122e070f` is present and paused PR #2
  commit `5f5bbf3c2aca0f55f35ae734c8dc0c6004897f75` is not an ancestor.
- Reused the pinned repository environment with Build123d 0.11.1 and OCP
  7.9.3.1. Doctor, catalog, all 30 canonical checksums, 174 lightweight tests,
  19 subtests, 84 CAD entrypoint checks, and lint passed without upgrades.
- Rejected job
  `20260723T224424-atomic-refactor-current-baseline-23a4a564a4` after its
  named base STEP was proven to be stale dirty-primary output. It differed from
  the accepted base by `4.6407331752 mm³`; no result from that job is baseline
  evidence.
- Correct-input job
  `20260723T231130-atomic-refactor-current-baseline-correct-input-593db9d217`
  used exact accepted base hash `441cc122...`, completed in 1482.206 seconds at
  1,400,373,248 bytes peak RSS, published ten outputs, and cleaned up without
  warnings or owned processes.
- Strict comparison job
  `20260723T234005-atomic-refactor-baseline-equivalence-008f589a51`
  completed in 2111.745 seconds at 2,492,252,160 bytes peak RSS. Both full
  solids and all six protected sections had matching topology/bounds/volume/
  area/center of mass and zero removed or added material at `1e-5 mm³`.
  Bucket/baffle overlap was zero and normalized validator/STEP-round-trip
  diagnostics matched exactly.
- The historical rail/equivalence blocker is therefore not current. The
  accepted flat-bottom missing-material relationship remains baseline behavior
  and will not be repaired during this refactor.

## 2026-07-23 — atom 01: parameter, print-contract and Variant I boundaries

- Added one native-free immutable Variant R parameter owner and replaced leaf
  literals/aliases for the active seam, bottom-ownership, fit and verification
  values.
- Added explicit rear-face-down bucket and +Z/brim baffle print metadata. These
  are print policies, not physical-print claims.
- Added an independent future Variant I boundary with open-bottom-down metadata
  and an explicit `NotImplementedError` geometry gate. It imports no Variant R
  module and creates no shape.
- Focused tests passed 12 cases. The complete lightweight suite passed 182
  tests, 19 subtests, catalog, 85 entrypoint checks, and lint.
- Candidate generation job
  `20260724T002420-atomic-refactor-atom-01-parameters-abc939b859`
  completed in 1475.821 seconds at 1,395,212,288 bytes peak RSS and published
  ten outputs with clean cleanup.
- Proportional geometry job
  `20260724T004959-atomic-refactor-atom-01-metrics-711d720604`
  completed in 1713.56 seconds at 1,090,289,664 bytes peak RSS. Validity,
  topology, bounds, volume, area and center of mass matched for both complete
  parts and all six protected sections; bucket/baffle overlap remained zero
  and normalized STEP-round-trip diagnostics matched.
- The release-grade baseline's strict bidirectional material result remains
  zero removed/added material. Atom 01 changed no native builder or interface,
  so its fresh proportional checkpoint intentionally did not repeat those
  expensive material Booleans.

## 2026-07-23 — atom 02: seam and bottom-material geometry ownership

- Extracted the exact authoritative-edge-reusing hybrid perimeter into
  `variant_r/seam.py`, the lower splice and print-edge transfer into
  `variant_r/bottom_ownership.py`, and their composition into
  `variant_r/assembly.py`.
- Added a minimal foundation protocol. New Variant R owners import no
  experiment, mutate no legacy global, and have no Variant I dependency.
- The existing deep cascade is contained behind a named leaf adapter; removing
  the leaf's disabled retention code and publishing a thin cataloged entrypoint
  is the next atom.
- The lightweight suite passed 186 tests, 19 subtests, catalog, 86 entrypoint
  checks, and lint.
- Candidate generation job
  `20260724T012509-atomic-refactor-atom-02-geometry-dcc2d21bcb`
  completed in 1495.143 seconds at 1,372,913,664 bytes peak RSS and published
  ten outputs with clean cleanup.
- Strict comparison job
  `20260724T015015-atomic-refactor-atom-02-strict-equivalence-68898b111a`
  completed in 2134.139 seconds at 2,377,777,152 bytes peak RSS. Both complete
  parts and all six protected sections matched validity, topology, bounds,
  volume, surface area and center of mass with zero removed/added material.
  Bucket/baffle overlap remained zero and normalized STEP-round-trip
  diagnostics matched.

## 2026-07-24 — atom 03: model/evidence/entrypoint ownership

- Removed the disabled hinge and bottom-screw alternatives and their feature
  flags. Retention geometry is now explicitly absent and remains a future
  geometry task.
- Added native-free Variant R model, artifact and verification owners, a thin
  cataloged entrypoint, and an explicit serialized legacy-runtime binding.
- The complete native-free suite passed 197 tests and 19 subtests in 5.898
  seconds; catalog validation reported 10 models and 38 experiment families,
  87 CAD entrypoints passed their safety audit, and scoped lint passed.
- Fresh generation job
  `20260724T023918-atomic-refactor-atom-03-geometry-06d4fd8a26`
  completed in 1515.502 seconds at 1,385,381,888 bytes peak RSS with ten
  outputs, no warnings and complete cleanup.
- Strict job
  `20260724T030459-atomic-refactor-atom-03-strict-equivalence-e9021d779e`
  completed in 2193.521 seconds at 2,533,801,984 bytes peak RSS. Both complete
  parts and all six protected sections match validity, topology, bounds,
  volume, surface area and center of mass and have zero bidirectional material
  difference. Bucket/baffle overlap is zero and normalized diagnostics match.
- A later independent review of the historical acceptance identified missing
  portable base-input, job-record and full-dependency provenance. Those gaps
  are now explicit final-acceptance work; no absent historic record is treated
  as current evidence.

## 2026-07-24 — atom 04: portable foundation and complete provenance

- Several plausible current-source foundation reconstructions were rejected
  because their topology or volume differed from the accepted input. The
  rejected attempts remain in `build/cad-jobs`; no candidate was normalized
  into acceptance.
- A capture-only run at immutable geometry commit `789cf7f` exported the
  untouched base immediately after its accepted construction boundary.
  Independent job
  `20260724T042646-historical-789-base-equivalence-d5f150a2ff` proved its
  complete STEP DATA section, topology, bounds, volume, surface area and center
  of mass equal to the accepted historical input. The generic OCCT symmetric
  difference was unstable for separately imported coincident copies and is
  recorded as unusable rather than reported as zero.
- The cataloged producer now archives that exact commit, applies the committed
  hash-bound overlay, and publishes only the base plus attestation through one
  supervised worker. Job
  `20260724T055629-atomic-refactor-atom-04-byte-identical-producer-aba03913c5`
  completed in 89.458 seconds at 1,297,514,496 bytes peak RSS.
- The generated STEP DATA was exact but its initial current export timestamp
  caused three tiny downstream diagnostic differences. Strict job
  `20260724T051716-atomic-refactor-atom-04-strict-equivalence-652ce28c58`
  rejected them. No tolerance was widened.
- The producer now verifies the full DATA payload and canonicalizes only the
  accepted STEP `FILE_NAME` timestamp, retaining the real job time separately
  in its attestation. The result is byte-identical at
  `441cc122c0383da257b16e80c4b424096f33b267cc95cab9d1278fb05a43a784`.
- The attestation binds 57 actually loaded repository sources, including 35
  geometry/parameter sources and all 33 loaded generator stages, to exact
  revisions and hashes. This replaces the historical nine-script fingerprint.
- Full validator job
  `20260724T055819-atomic-refactor-atom-04-byte-identical-geometry-8764c19346`
  completed in 1498.687 seconds at 1,401,372,672 bytes peak RSS. Strict job
  `20260724T062345-atomic-refactor-atom-04-byte-identical-strict-97ee20c79b`
  completed in 2093.563 seconds at 2,458,206,208 bytes peak RSS. Both complete
  parts and all six sections matched every deterministic measurement with zero
  removed/added material and zero-volume mating contact.

## 2026-07-24 — atom 05: deterministic measurement ownership

- Moved native topology/mass/material/intersection measurement serialization
  into `variant_r/measurements.py` and native-free acceptance predicates into
  `variant_r/equivalence.py`. Workbench scripts are now evidence adapters only.
- Geometry builders, the immutable producer, toolchain, settings and all
  current artifacts were unchanged, so the immediately preceding strict
  checkpoint is a verified geometry cache hit. Lightweight checks passed 208
  tests and 19 subtests, 89 entrypoints, catalog and lint.

## 2026-07-24 — atom 06: STEP export ownership

- Moved coordinated STEP publication, settings, reimport and intermediate
  stabilization into `variant_r/export.py`. The validator no longer owns
  duplicated STEP round-trip logic.
- No builder, parameter, transform or artifact contract changed. Lightweight
  checks passed 209 tests and 19 subtests, 89 entrypoints, catalog and lint.
  The final forced release will exercise the moved measurement and export
  adapters together before visual review.

## 2026-07-24 — forced final release and visual checkpoint

- Clean producer job
  `20260724T071800-atomic-refactor-final-producer-fa1def52ae` completed in
  88.419 seconds at 1,235,189,760 bytes peak RSS. It reproduced accepted input
  hash `441cc122...` byte-for-byte and published fresh attestation
  `0d2ae5c4...`, bound to clean source commit `5a076262...` and all 57 loaded
  repository sources (35 geometry/parameter sources; 33 loaded generator
  stages).
- Forced release job
  `20260724T071935-atomic-refactor-final-release-5a33762429` completed in
  1471.811 seconds at 1,382,973,440 bytes peak RSS and atomically published ten
  outputs. Strict job
  `20260724T074434-atomic-refactor-final-strict-0e704345d5` completed in
  2069.819 seconds at 2,446,458,880 bytes peak RSS. Report `24527601...`
  passes both complete parts and all six sections with matching deterministic
  measurements, zero removed/added material, matching normalized diagnostics,
  zero-volume mating contact and STEP round trips.
- Final native-free job
  `20260724T081949-atomic-refactor-final-lightweight-26832f42e1` completed in
  6.112 seconds at 21,659,648 bytes peak RSS: 209 tests plus 19 subtests,
  catalog 10/38, 89 entrypoints and lint all pass.
- Visual review assembly job
  `20260724T082056-atomic-refactor-final-review-assembly-ac5c8ca527` packaged
  the exact bucket and baffle in design coordinates at hash `cfd4ad3...`.
  Sidecar job `20260724T082106-text-to-cad-artifacts-9f8b4acb3a` produced
  `94c143c...`. Snapshot job
  `20260724T082321-text-to-cad-artifacts-bf297483aa` produced inspected
  isometric `9150298...` and bottom detail `73b5eeb...`. The first Snapshot
  attempt failed before geometry import because the clean worktree lacked its
  pinned runtime; the second sandboxed attempt exposed the expected macOS
  Chromium permission failure. The successful job reused the pinned runtime
  from the primary tool checkout and ran with the required local launch
  permission. No tool was installed or upgraded.
- The agent inspected both direct Snapshot outputs. The overview shows the
  expected assembled envelope, removable front, driver opening, port and
  visible seam with no detached or misplaced body. The bottom view shows the
  preserved imperfect lower/front contour with no detached body. These are
  visual observations only; measurable claims remain bound to deterministic
  evidence. No human visual attestation has been supplied.

## 2026-07-24 — landing: observational release provenance and final gates

- Amended release provenance introduced before the serialized legacy geometry
  process changed the release diagnostics. Strict job
  `20260724T090914-atomic-refactor-final2-strict-894348d891` failed closed; no
  tolerance was widened and its removed staged report is not represented as
  current evidence.
- Commits `d114d79` and `3885932` restored the exact previously proven
  validator/import path and moved release provenance into a separate
  observational job. The validator and four pre-geometry Variant R modules are
  byte-identical to their pre-regression versions.
- Restored release job
  `20260724T102722-atomic-refactor-landing-restored-release-52bd80460c`
  completed in 1493.266 seconds at 1,403,142,144 bytes peak RSS. Observational
  attestation job
  `20260724T115857-atomic-refactor-review-release-attestation-74aaf7c31f`
  binds release commit `d114d79`, exact release-job record `ca4ba25a...`, nine
  model artifacts, the exact portable input, 62 runtime sources, 58
  geometry/parameter sources and all 33 generator stages without entering the
  geometry process. Every dependency byte matches the commit. The release job
  did not record whole-tree cleanliness, and the evidence does not claim it.
- Strict job `20260724T105504-atomic-refactor-landing-strict-a9945e2f37`
  passed in 2113.045 seconds at 2,430,173,184 bytes peak RSS. Report
  `2cc8b236...` proves both parts and all six sections equivalent with zero
  bidirectional material delta, matching diagnostics and zero-volume contact.
- Lightweight job
  `20260724T115821-atomic-refactor-review-fixes-lightweight-3f0e3043be`
  passed 212 tests plus 19 subtests, catalog 10/38, 91 entrypoints and lint in
  6.609 seconds at 21,807,104 bytes peak RSS.
- Exact review assembly `a1211ad...`, attestation `30387b5...`, and sidecar
  `5914ddf...` bind the final release. Snapshot job
  `20260724T113322-atomic-refactor-landing-snapshot-292020a205` produced
  inspected overview `9150298...` and bottom detail `73b5eeb...`, byte-identical
  to the prior continuity images. The bottom imperfection remains intentionally
  preserved. No human visual attestation has been supplied.

## 2026-07-24 — independent adversarial landing review

- Initial read-only review of exact base `c25cddb...` to candidate `f91b85d...`
  reported one compatibility-architecture Blocker, two evidence Should-fix
  findings, and one documentation Nit.
- Commit `9d5fef5` restored the immutable baseline record and made release
  evidence independently verify the exact job JSON, coordinated validator, all
  nine artifacts, and all 62 dependency bytes at release commit `d114d79`.
  Commits `a52e4e4` and `e1c22b7` bound those facts and documented the
  serialized compatibility limitation, its safety evidence, and its separate
  follow-up scope.
- The same reviewer re-reviewed exact base `c25cddb...` to amended candidate
  `e1c22b7...` under the binding landing ruling. Final result: zero Blockers,
  zero Should-fix findings, zero Nits, and no unresolved actionable findings.
  It found no evidence that the serialized path is unsafe in production or
  geometry-nondeterministic and confirmed paused PR #2 remains absent.
