jaspercurry/sand-cube/cad_verification/README.md

# CAD verification core

`cad_verification` is a standard-library-only contract and review-packet core.
It deliberately does not import Build123d, OCP, `cad_runner`, Viewer code, or a
repository model.  Production integrations provide measurements and artifact
observations through the protocols in `protocols.py`.

The Python dataclasses in `model.py` are the authoritative contract and report
representation.  JSON is a deterministic serialization of those classes, not
a second hand-maintained schema.  `policy.py` is the sole vocabulary and policy
catalog for profiles, checks, units, statuses, and evidence routing.  Consumers
should inspect `PROFILE_POLICIES`, `CHECK_POLICIES`, and `EVIDENCE_POLICIES`
instead of copying their meanings.

The main flow is:

1. construct or deserialize a `DesignContract` and call
   `assert_valid_contract`;
2. select work with `requirements_for_profile`;
3. let an external adapter measure each requirement and pass its actual value
   to `assess` (or explicitly return `unverified`);
4. construct a `ReviewPacket` and call `assert_valid_review_packet`;
5. persist it with `review_packet_to_json` and use `profile_status` for the
   profile outcome.

`examples.py` provides a complete synthetic contract and release review packet
without touching native CAD.

A PASS-eligible packet binds every artifact to a successful, zero-exit,
fully-cleaned execution record with repository-relative output hashes. Snapshot
claims name the rendered PNG, its source STEP and sidecar, and an explicit
inspection attestation. Viewer claims name a probed read-only session record.
Those fields are defined only by the dataclasses in
[`model.py`](model.py) and enforced by [`validation.py`](validation.py); there
is no parallel hand-written JSON schema.

Repository users validate and inspect these objects through
`scripts/cad_review.py verify`. The authoritative profile/check/evidence policy
is [`policy.py`](policy.py); CLI and repository adapters consume that policy and
must not restate it.

## Compact iteration state

[`workflow.py`](workflow.py) provides a second, deliberately small model for
live AI CAD task state. It points to the durable brief, contract, sources, and
evidence by repository-relative path and SHA-256. It does not copy their
geometry facts or acceptance criteria.

The ordered gates are candidate, fast passed, visual accepted, fit passed,
release passed, and independently reviewed. Source changes start a new revision
and clear downstream evidence. `scripts/cad_review.py workflow` is the thin CLI
for initializing, showing, gating, advancing, and revising this state.
