jaspercurry/sand-cube/workbench/designs/atomic_characterization_refactor/independent-review.md

# Independent adversarial review

- Exact base: `c25cddb3eeafe6f6dff3b551be4ceb53d5aee9ce`
- Initial candidate: `f91b85df767d8d3d7d199262b63d37f3ae54323c`
- Amended candidate:
  `e1c22b75ec20a86bf576490f224c2b6bea919f92`
- Reviewer: independent read-only sub-agent `/root/adversarial_review`
- Paused PR #2 commit:
  `5f5bbf3c2aca0f55f35ae734c8dc0c6004897f75` is not an ancestor.

## Initial findings

1. **Blocker:** visible serialized temporary bindings into the historical
   experiment cascade did not meet the aspirational no-monkeypatching target.
2. **Should-fix:** `current-baseline-evidence.json` mixed exact-base identity
   with later candidate facts.
3. **Should-fix:** the release attestation accepted job, artifact and commit
   identities without independently validating every bound fact.
4. **Nit:** the release-provenance docstring described the superseded
   in-validator collection path.

## Amendments

- `9d5fef53073efcfb2e91baed27829c0644f5682f` restores the historical
  baseline record byte-for-byte, verifies the exact completed release-job JSON
  and expected coordinated validator, verifies all nine artifact paths, hashes
  and byte counts, verifies all 62 dependency source hashes and byte counts at
  release commit `d114d79`, and corrects the provenance description.
- `a52e4e4` commits the amended attestation projection and honestly records
  that the historical release job did not capture whole-tree cleanliness.
- `e1c22b75ec20a86bf576490f224c2b6bea919f92` records the binding landing
  scope and the compatibility evidence: one `RLock`, identity-checked
  restoration, two identical in-process seam fingerprints, two successful
  restoration cycles, strict geometry/diagnostic equivalence, a scoped unit
  test, coordinated entrypoints and production concurrency limit 1.
- A full historical-cascade dependency-injection rewrite remains a separately
  scoped architecture follow-up. The landing does not claim that the temporary
  binding mechanism satisfies the aspirational no-monkeypatching target.

## Final re-review

The same reviewer inspected the exact
`c25cddb3eeafe6f6dff3b551be4ceb53d5aee9ce..e1c22b75ec20a86bf576490f224c2b6bea919f92`
diff and reported:

- Blockers: none.
- Should-fix findings: none.
- Nits: none.
- No unresolved actionable findings within the agreed landing scope.
- No evidence that the serialized compatibility path is unsafe in production
  or geometry-nondeterministic.
- The amended delta is observational provenance, evidence, tests and records;
  it introduces no geometry redesign.

Final disposition: **ready to land within the stated no-geometry-change
scope**.
