jaspercurry/sand-cube/workbench/designs/atomic_characterization_refactor/dependency_graph.md

<!-- Generated by render_phase_a_reports.py from atomic_manifest.json. Do not edit by hand. -->

# Dependency graph

Authority: atom dependency and consumer fields in `atomic_manifest.json`.

```mermaid
flowchart LR
  family_coordinate_contract["family.coordinate_contract"]
  family_exterior_envelope["family.exterior_envelope"]
  family_exterior_shell["family.exterior_shell"]
  family_inner_wall_sand_void["family.inner_wall_sand_void"]
  family_rear_face["family.rear_face"]
  R_front_service_opening["R.front_service_opening"]
  R_front_bulkhead_gasket_support["R.front_bulkhead_gasket_support"]
  R_sculpted_lrt_seam["R.sculpted_lrt_seam"]
  R_bottom_material_ownership["R.bottom_material_ownership"]
  R_baffle_body["R.baffle_body"]
  R_flat_baffle_print_edge["R.flat_baffle_print_edge"]
  family_driver_interface["family.driver_interface"]
  R_gasket_land_compression["R.gasket_land_compression"]
  R_corner_sealing["R.corner_sealing"]
  family_fill_blisters_passages["family.fill_blisters_passages"]
  family_braces_supports["family.braces_supports"]
  family_support_sensitive_transitions["family.support_sensitive_transitions"]
  R_bucket_print_contract["R.bucket_print_contract"]
  R_baffle_print_contract["R.baffle_print_contract"]
  I_integral_front["I.integral_front"]
  I_open_bottom["I.open_bottom"]
  I_hatch_interface["I.hatch_interface"]
  I_print_contract["I.print_contract"]
  R_hinge_interface["R.hinge_interface"]
  R_fastener_interface["R.fastener_interface"]
  deferred_horn_interface["deferred.horn_interface"]
  deferred_tube_interface["deferred.tube_interface"]
  deferred_resonator_interface["deferred.resonator_interface"]
  deferred_bracket_interface["deferred.bracket_interface"]
  deferred_electronics_interface["deferred.electronics_interface"]
  family_coordinate_contract --> family_exterior_envelope
  family_coordinate_contract --> family_exterior_shell
  family_exterior_envelope --> family_exterior_shell
  family_exterior_shell --> family_inner_wall_sand_void
  family_exterior_shell --> family_rear_face
  family_inner_wall_sand_void --> family_rear_face
  family_exterior_shell --> R_front_service_opening
  family_inner_wall_sand_void --> R_front_service_opening
  R_front_service_opening --> R_front_bulkhead_gasket_support
  family_inner_wall_sand_void --> R_front_bulkhead_gasket_support
  R_front_service_opening --> R_sculpted_lrt_seam
  R_front_bulkhead_gasket_support --> R_sculpted_lrt_seam
  R_front_service_opening --> R_bottom_material_ownership
  family_exterior_shell --> R_bottom_material_ownership
  R_sculpted_lrt_seam --> R_baffle_body
  R_bottom_material_ownership --> R_baffle_body
  family_driver_interface --> R_baffle_body
  R_baffle_body --> R_flat_baffle_print_edge
  R_bottom_material_ownership --> R_flat_baffle_print_edge
  family_coordinate_contract --> family_driver_interface
  R_sculpted_lrt_seam --> R_gasket_land_compression
  R_front_bulkhead_gasket_support --> R_gasket_land_compression
  R_baffle_body --> R_gasket_land_compression
  R_front_bulkhead_gasket_support --> R_corner_sealing
  R_gasket_land_compression --> R_corner_sealing
  family_inner_wall_sand_void --> family_fill_blisters_passages
  R_front_bulkhead_gasket_support --> family_fill_blisters_passages
  family_inner_wall_sand_void --> family_braces_supports
  deferred_tube_interface --> family_braces_supports
  family_braces_supports --> family_support_sensitive_transitions
  family_fill_blisters_passages --> family_support_sensitive_transitions
  family_rear_face --> R_bucket_print_contract
  family_support_sensitive_transitions --> R_bucket_print_contract
  R_front_service_opening --> R_bucket_print_contract
  R_flat_baffle_print_edge --> R_baffle_print_contract
  family_support_sensitive_transitions --> R_baffle_print_contract
  family_exterior_shell --> I_integral_front
  family_driver_interface --> I_integral_front
  family_fill_blisters_passages --> I_integral_front
  I_integral_front --> I_open_bottom
  family_inner_wall_sand_void --> I_open_bottom
  I_open_bottom --> I_hatch_interface
  I_open_bottom --> I_print_contract
  family_support_sensitive_transitions --> I_print_contract
  R_sculpted_lrt_seam --> R_hinge_interface
  R_baffle_body --> R_hinge_interface
  R_bottom_material_ownership --> R_fastener_interface
  R_gasket_land_compression --> R_fastener_interface
  family_exterior_envelope --> deferred_horn_interface
  family_driver_interface --> deferred_horn_interface
  family_inner_wall_sand_void --> deferred_tube_interface
  family_rear_face --> deferred_tube_interface
  deferred_tube_interface --> deferred_resonator_interface
  family_driver_interface --> deferred_bracket_interface
  deferred_horn_interface --> deferred_bracket_interface
  family_exterior_shell --> deferred_electronics_interface
  family_inner_wall_sand_void --> deferred_electronics_interface
```

Deferred external components terminate at interface atoms; no acoustic or product geometry is integrated by this map.
